giltesa/Game-Boy-Color-USB-C-charging-kit/4. Photos/v1.5/IMG_20201130_193659.jpg

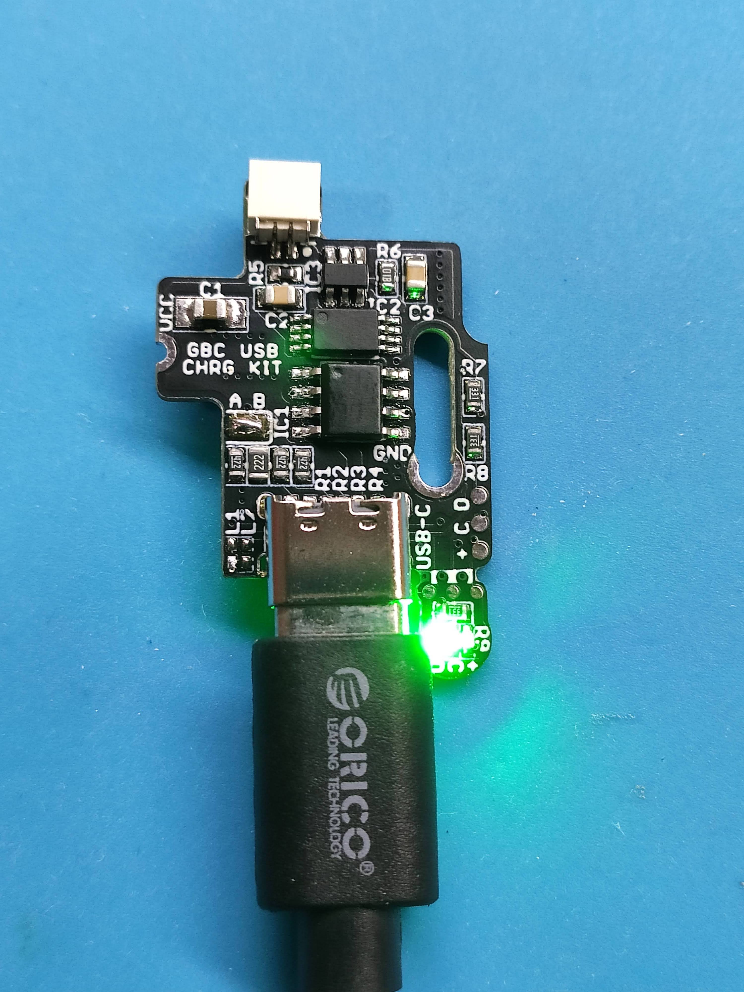
4. Photos/v1.5/IMG_20201130_193659.jpg
